peterpolidoro/wingbeat_detector/documentation/filter/high-pass-filter-block-diagram.png

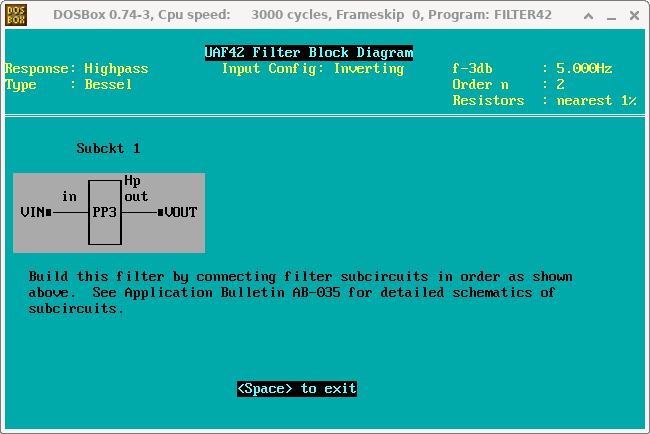
documentation/filter/high-pass-filter-block-diagram.png
