peterpolidoro/wingbeat_detector/documentation/filter/high-pass-filter-design.png

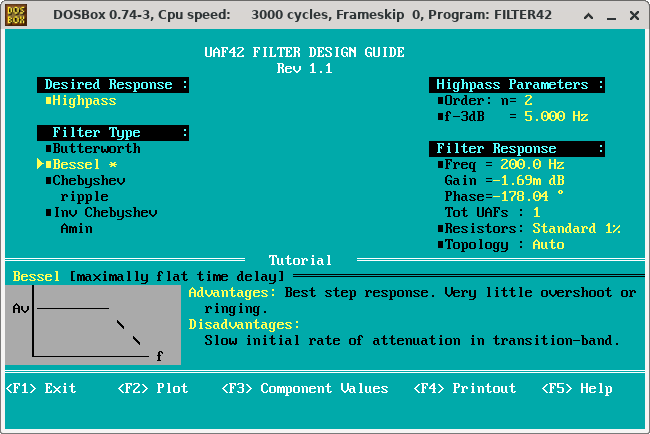
documentation/filter/high-pass-filter-design.png
