peterpolidoro/wingbeat_detector/documentation/filter/high-pass-filter-plot.png

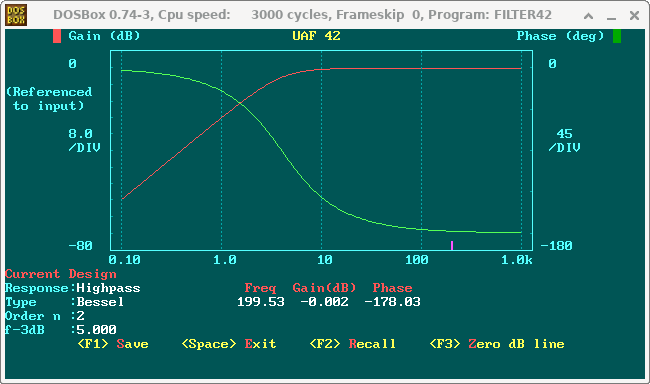
documentation/filter/high-pass-filter-plot.png
