peterpolidoro/wingbeat_detector/documentation/pcb/back.png

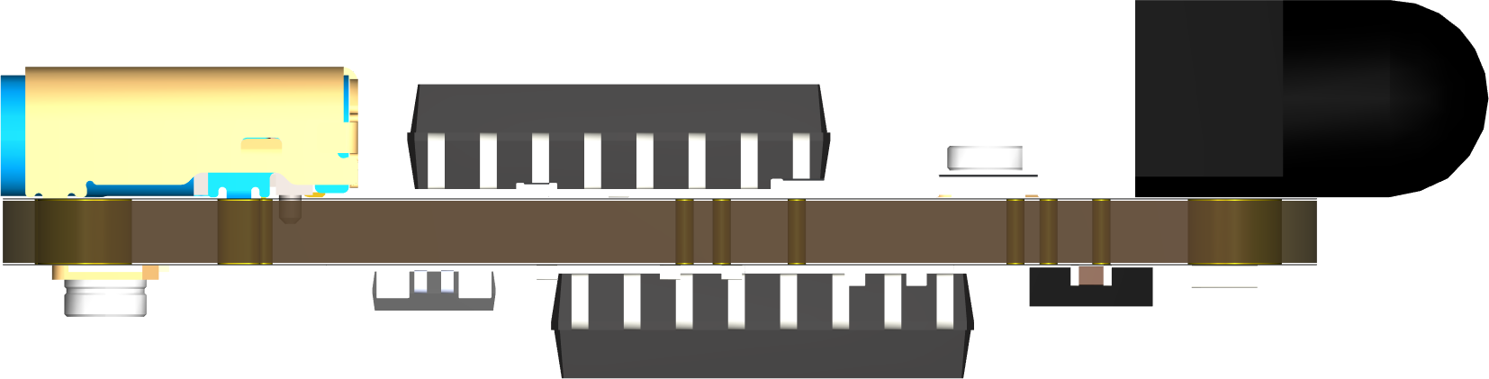
documentation/pcb/back.png
