peterpolidoro/wingbeat_detector/documentation/pcb/bottom.png

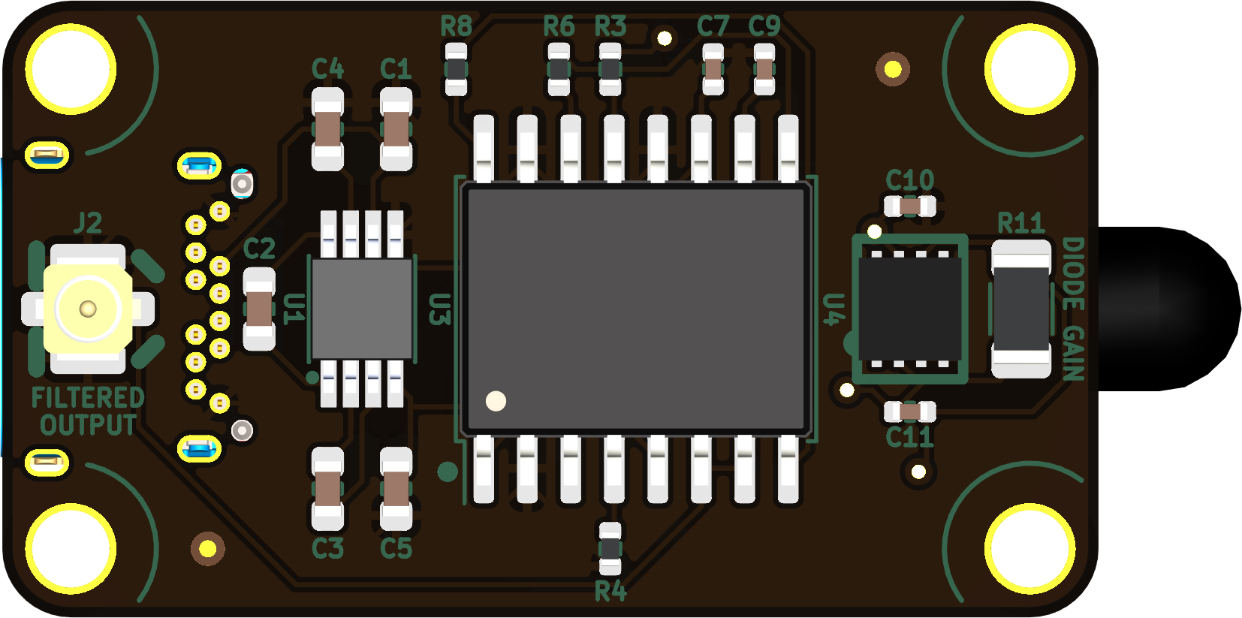
documentation/pcb/bottom.png
