peterpolidoro/wingbeat_detector/documentation/pcb/left.png

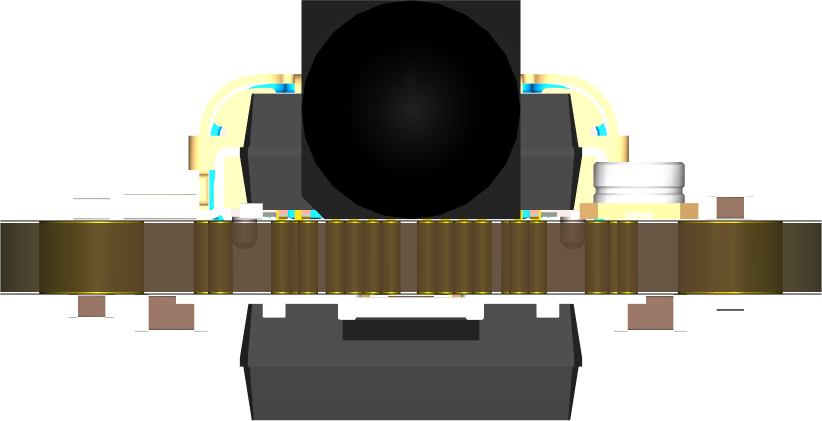
documentation/pcb/left.png
