peterpolidoro/wingbeat_detector/documentation/pcb/right.png

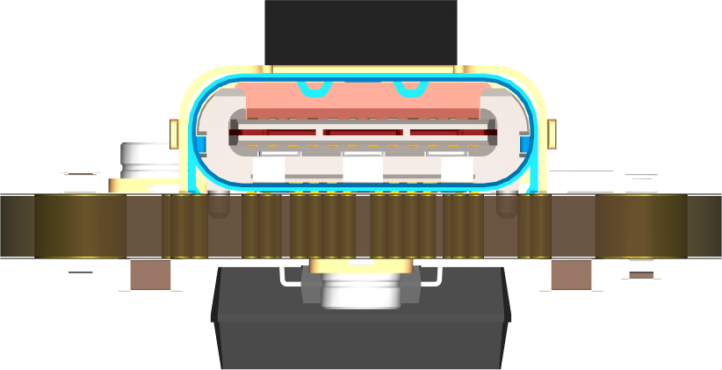
documentation/pcb/right.png
