peterpolidoro/wingbeat_detector/documentation/pcb/top.png

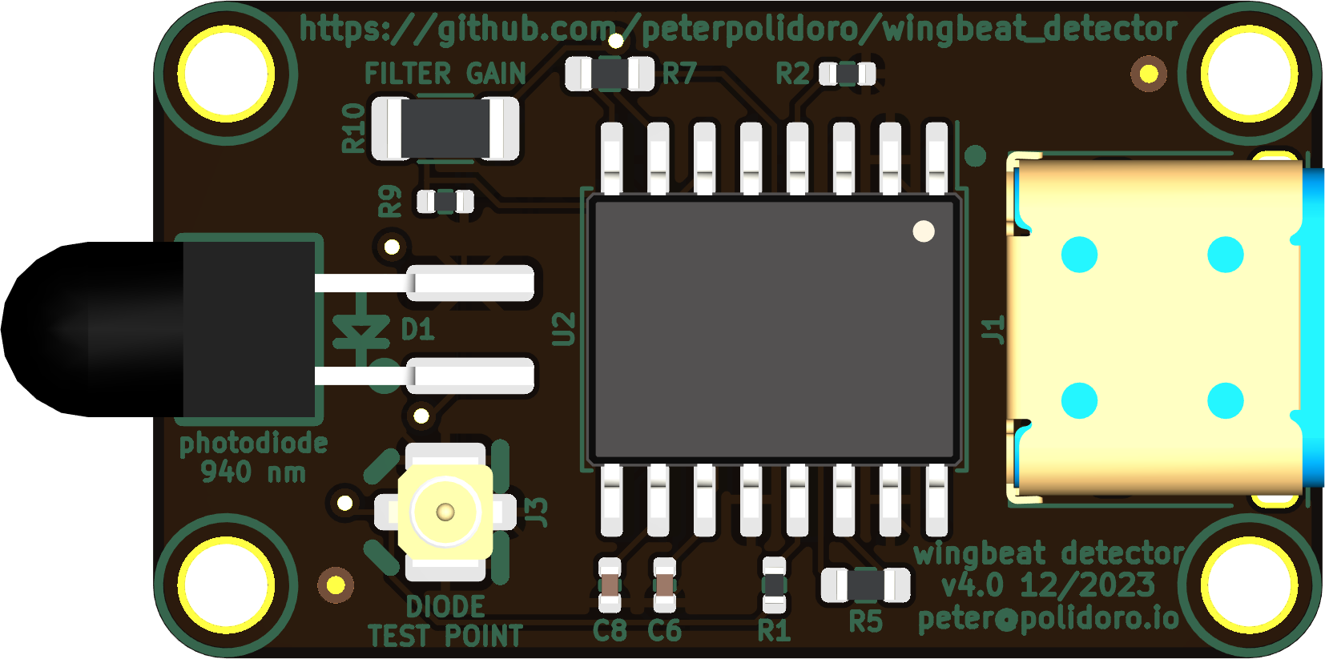
documentation/pcb/top.png
