peterpolidoro/wingbeat_detector/documentation/filter/high-pass-filter-components.png

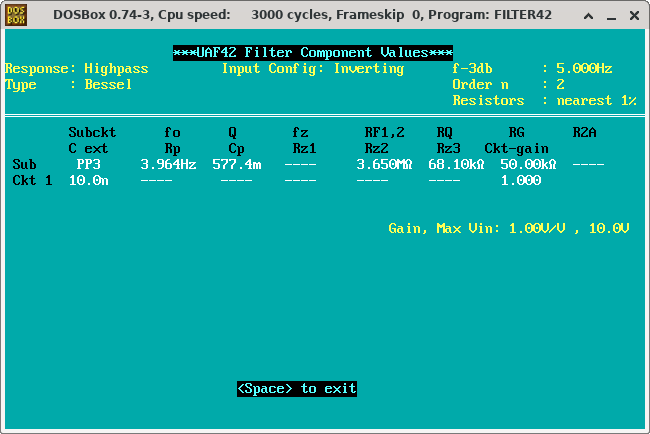
documentation/filter/high-pass-filter-components.png
