peterpolidoro/wingbeat_detector/documentation/3dmodels/step/nut.step

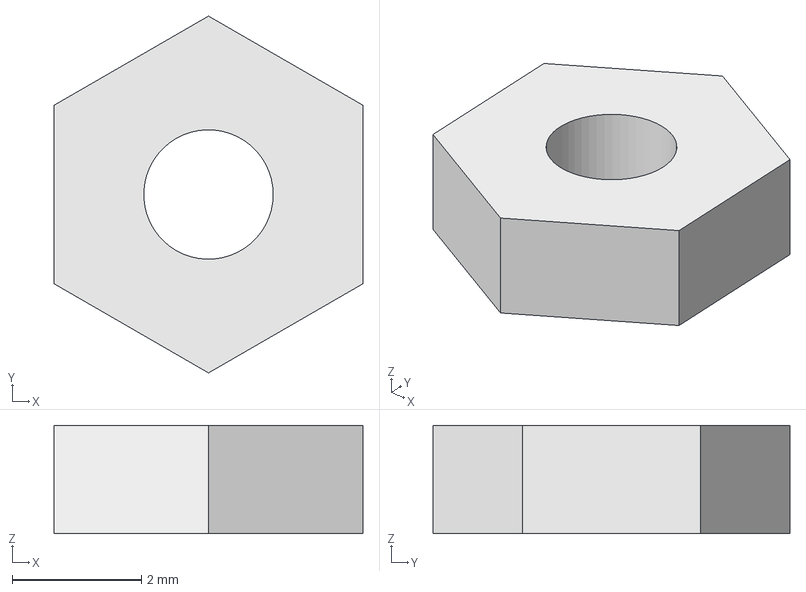
[picture p29: CAD file, 2024-02-15]
documentation/3dmodels/step/nut.step
4.78 x 5.51 x 1.68 mm
