peterpolidoro/wingbeat_detector/documentation/3dmodels/step/screw.step

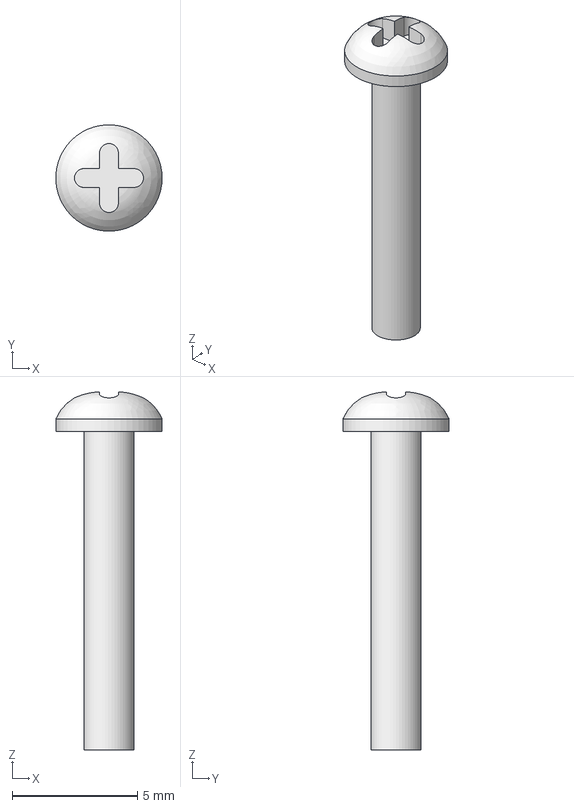
[picture p30: CAD file, 2024-02-15]
documentation/3dmodels/step/screw.step
4.24 x 4.24 x 14.3 mm
