peterpolidoro/wingbeat_detector/documentation/assembly/assembly0.png

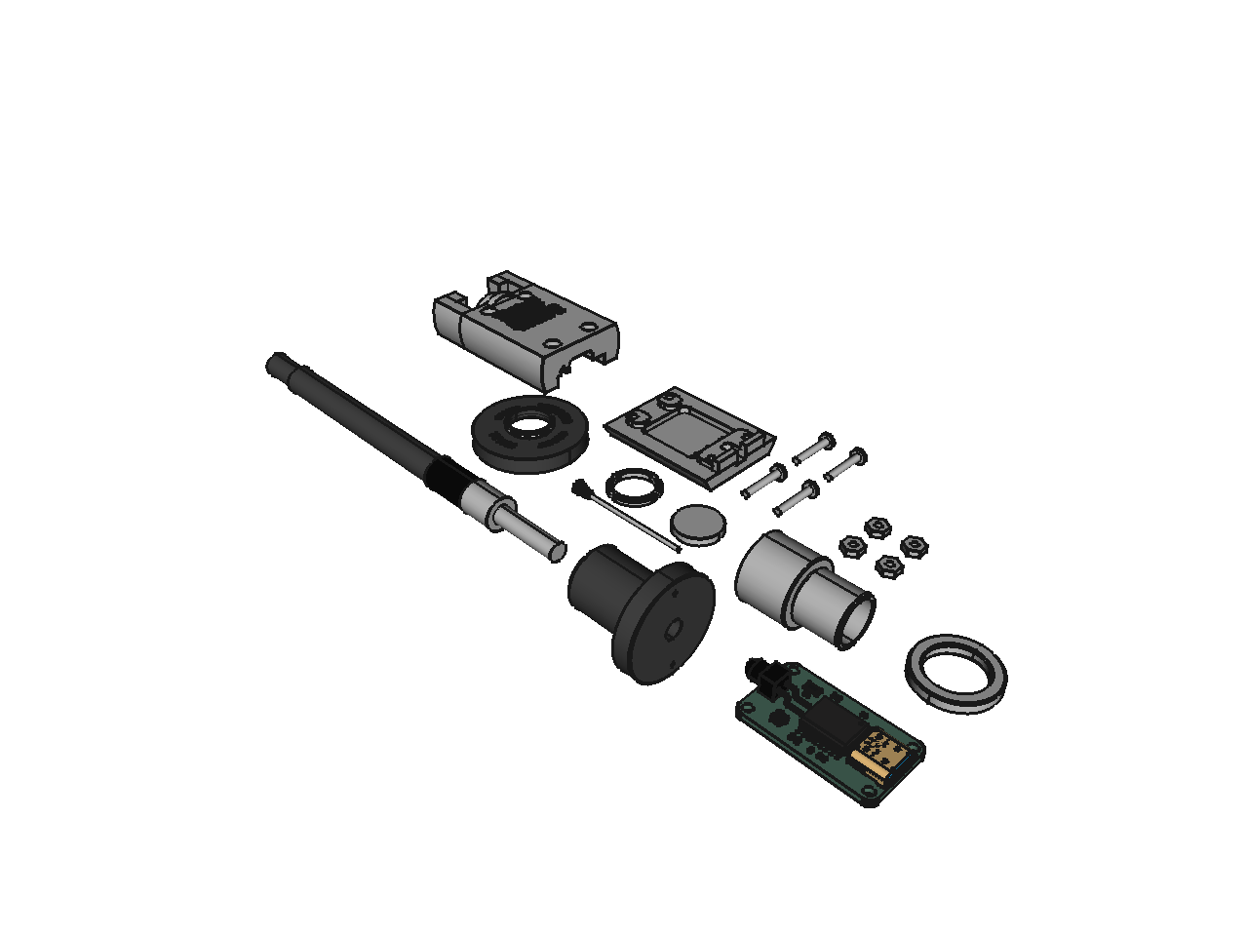
documentation/assembly/assembly0.png
